dimhoff/sensof/software/firmware/src/crc.c

/**
 * crc_simple.c - Simple/Naive implementations of the CRC algorithm
 *
 * Written 2014, David Imhoff <dimhoff.devel@gmail.com>
 *
 * This is free and unencumbered software released into the public domain.
 * 
 * Anyone is free to copy, modify, publish, use, compile, sell, or
 * distribute this software, either in source code form or as a compiled
 * binary, for any purpose, commercial or non-commercial, and by any
 * means.
 * 
 * In jurisdictions that recognize copyright laws, the author or authors
 * of this software dedicate any and all copyright interest in the
 * software to the public domain. We make this dedication for the benefit
 * of the public at large and to the detriment of our heirs and
 * successors. We intend this dedication to be an overt act of
 * relinquishment in perpetuity of all present and future rights to this
 * software under copyright law.
 * 
 * THE SOFTWARE IS PROVIDED "AS IS", WITHOUT WARRANTY OF ANY KIND,
 * EXPRESS OR IMPLIED, INCLUDING BUT NOT LIMITED TO THE WARRANTIES OF
 * MERCHANTABILITY, FITNESS FOR A PARTICULAR PURPOSE AND NONINFRINGEMENT.
 * IN NO EVENT SHALL THE AUTHORS BE LIABLE FOR ANY CLAIM, DAMAGES OR
 * OTHER LIABILITY, WHETHER IN AN ACTION OF CONTRACT, TORT OR OTHERWISE,
 * ARISING FROM, OUT OF OR IN CONNECTION WITH THE SOFTWARE OR THE USE OR
 * OTHER DEALINGS IN THE SOFTWARE.
 */
#include "crc.h"

#include <stdbool.h>

#define CRC_8_DALLAS_POLY 0x31
#define CRC_16_POLY 0x8005

uint8_t crc8(uint8_t crc, uint8_t b)
{
	uint8_t i=8;
	bool do_xor;

	while (i) {
		do_xor = (b ^ crc) & 0x80;

		crc = crc << 1;

		if (do_xor) {
			crc ^= CRC_8_DALLAS_POLY;
		}

		b = b << 1;
		i--;
	}
      
	return crc;
}

uint16_t crc16(uint16_t crc, uint8_t b)
{
	uint8_t i=8;
	bool do_xor;

	while (i) {
		do_xor = (b ^ (crc >> 8)) & 0x80;

		crc = crc << 1;

		if (do_xor) {
			crc ^= CRC_16_POLY;
		}

		b = b << 1;
		i--;
	}
      
	return crc;
}
