dimhoff/sensof/software/firmware/src/stdint.h

#ifndef __STDINT_H__
#define __STDINT_H__

typedef signed char int8_t;
typedef unsigned char uint8_t;

typedef signed int int16_t;
typedef unsigned int uint16_t;

typedef signed long int int32_t;
typedef unsigned long int uint32_t;

#endif //__STDINT_H__
